GustavAbrahamsson/George-the-Hexapod/CAD/Prototype leg 1/MG996R servo holder v7.stl

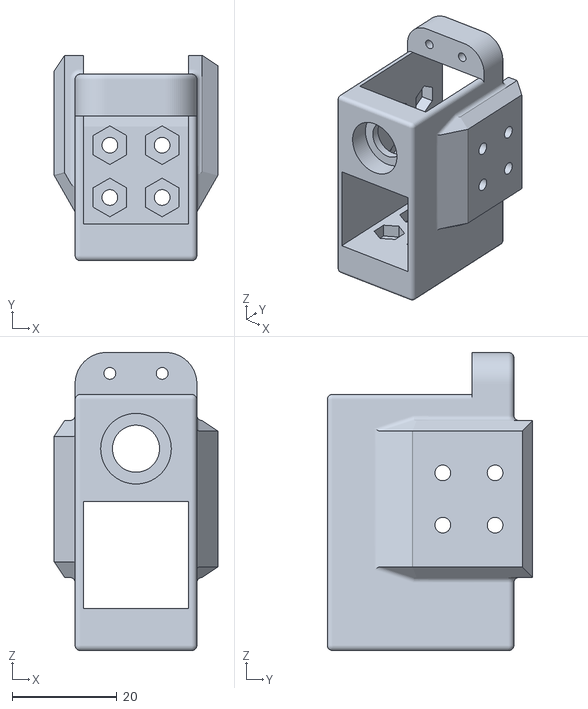
[picture p19: CAD file, 2021-05-09]
CAD/Prototype leg 1/MG996R servo holder v7.stl
31.3 x 39.3 x 57.0
