GustavAbrahamsson/George-the-Hexapod/CAD/Prototype leg 3/Powerbank holder.stl

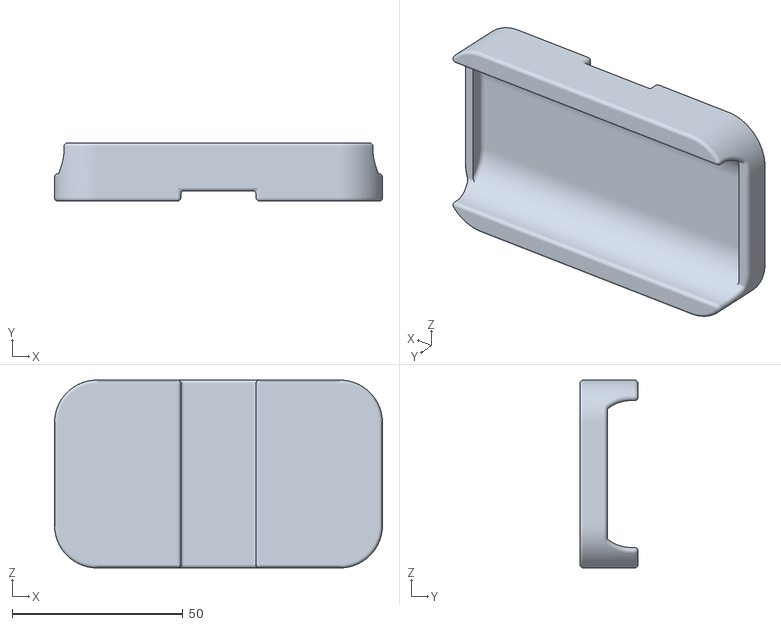
[picture p20: CAD file, 2021-05-09]
CAD/Prototype leg 3/Powerbank holder.stl
96.0 x 17.0 x 55.0
