GustavAbrahamsson/George-the-Hexapod/CAD/Prototype leg 1/Tibia v9.stl

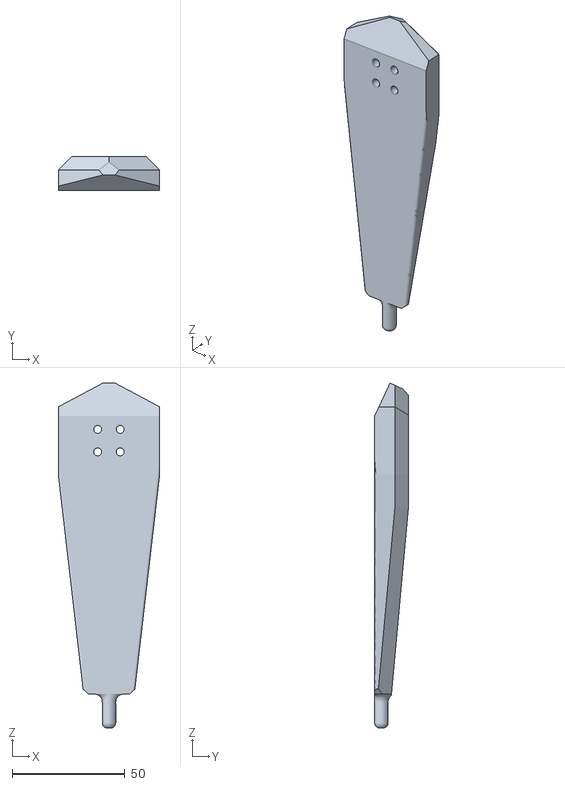
[picture p21: CAD file, 2021-05-09]
CAD/Prototype leg 1/Tibia v9.stl
45.0 x 15.0 x 153.1
