GustavAbrahamsson/George-the-Hexapod/CAD/Prototype leg 3/FemurSec.stl

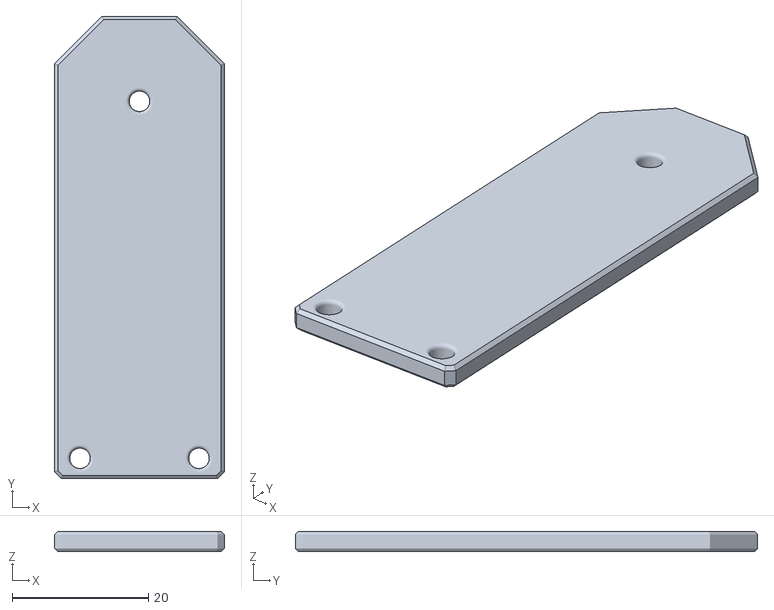
[picture p22: CAD file, 2021-05-09]
CAD/Prototype leg 3/FemurSec.stl
25.0 x 68.0 x 3.00
