GustavAbrahamsson/George-the-Hexapod/CAD/Prototype leg 3/Powerbank holder v9.stl

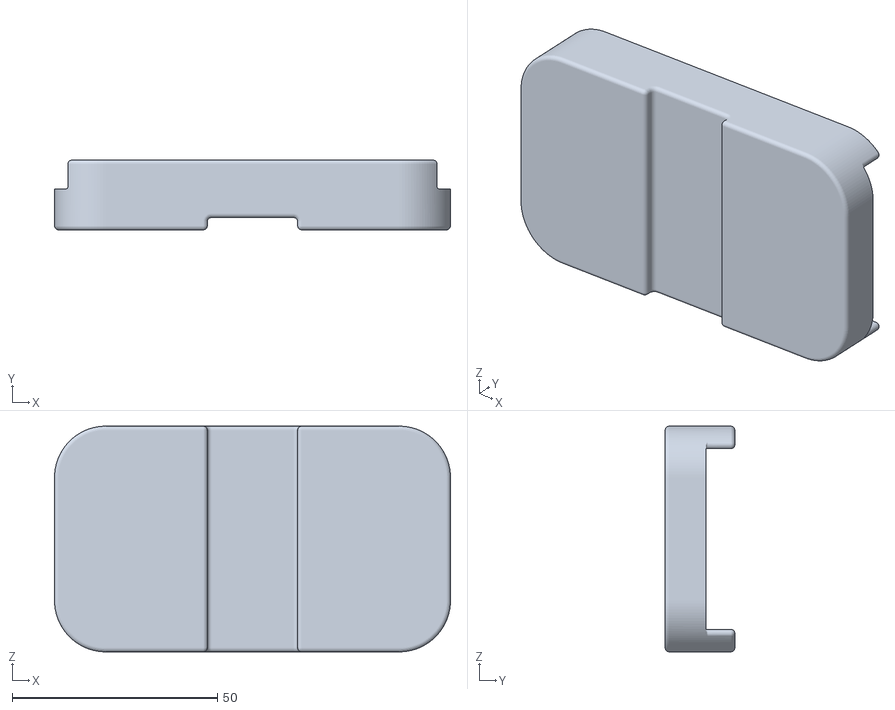
[picture p23: CAD file, 2021-05-09]
CAD/Prototype leg 3/Powerbank holder v9.stl
96.5 x 17.0 x 55.0
