GustavAbrahamsson/George-the-Hexapod/CAD/Prototype leg 2/Tibia v13.stl

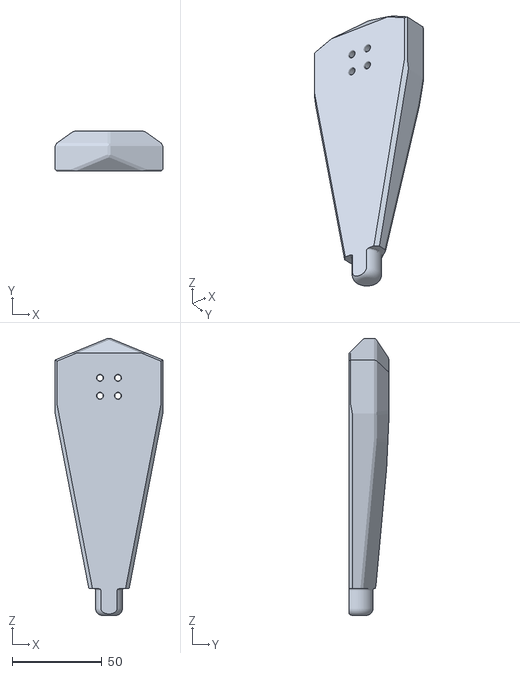
[picture p24: CAD file, 2021-05-09]
CAD/Prototype leg 2/Tibia v13.stl
60.0 x 22.5 x 154.5
