GustavAbrahamsson/George-the-Hexapod/CAD/Prototype leg 3/CoxaSec.stl

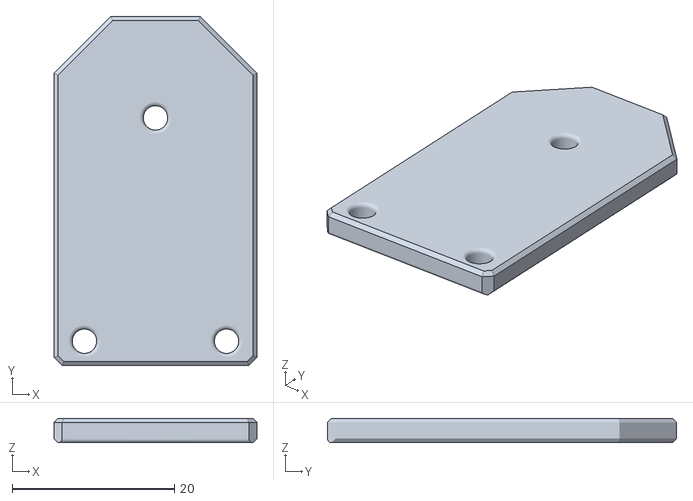
[picture p25: CAD file, 2021-05-09]
CAD/Prototype leg 3/CoxaSec.stl
25.0 x 43.0 x 3.00
